Miceuz/linear-led-dimmer/doc/pics/DSC01135.JPG

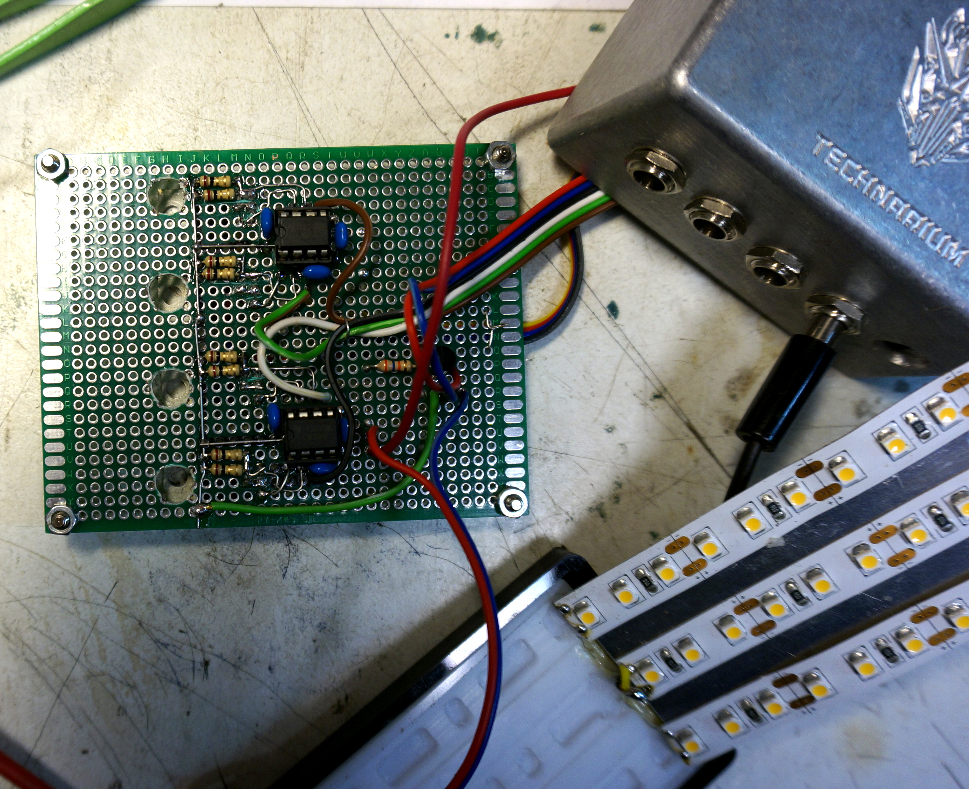
doc/pics/DSC01135.JPG
