Miceuz/linear-led-dimmer/doc/pics/DSC01143.JPG

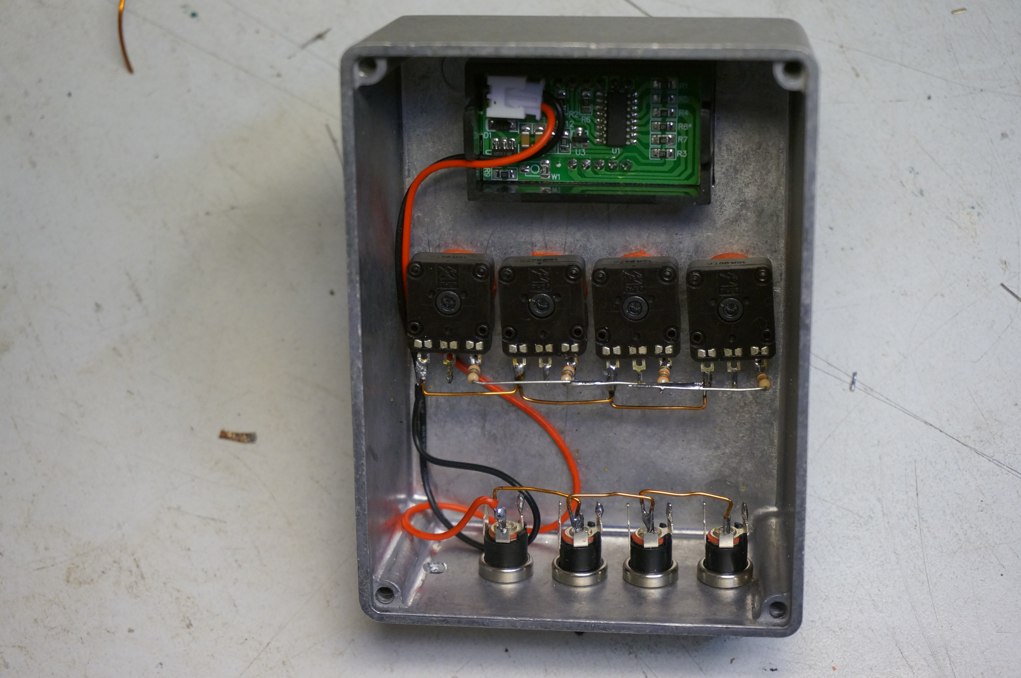
doc/pics/DSC01143.JPG
