Miceuz/linear-led-dimmer/doc/pics/DSC01162.JPG

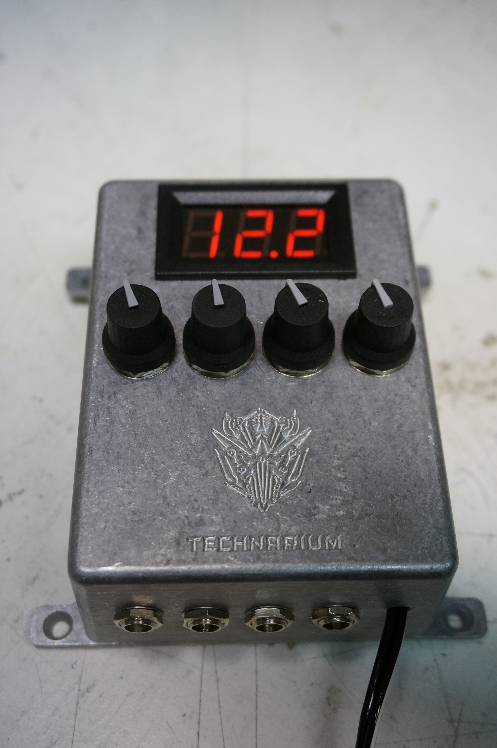
doc/pics/DSC01162.JPG
