Miceuz/linear-led-dimmer/linear-dimmer-back.png

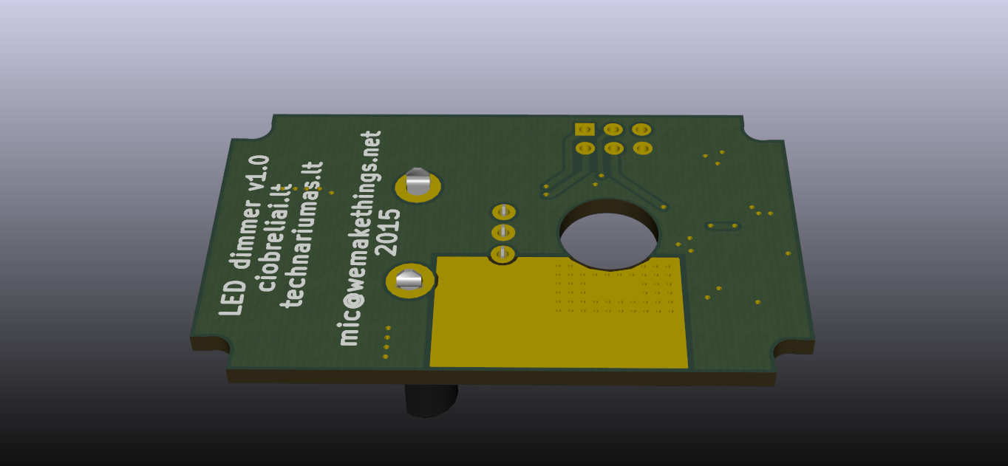
linear-dimmer-back.png
