Miceuz/linear-led-dimmer/linear-dimmer-v2.0-long-edge-conn-back.png

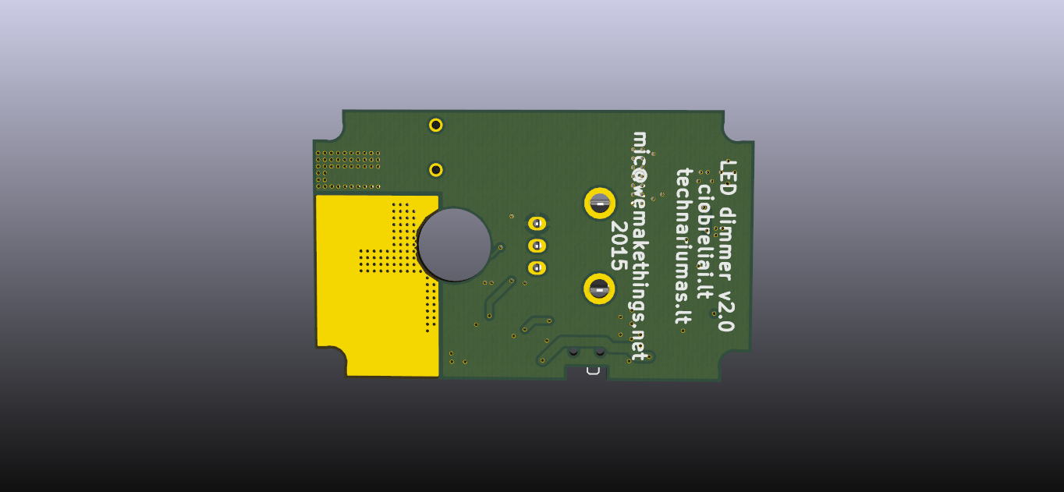
linear-dimmer-v2.0-long-edge-conn-back.png
