Miceuz/linear-led-dimmer/linear-dimmer-v2.0-ortho.png

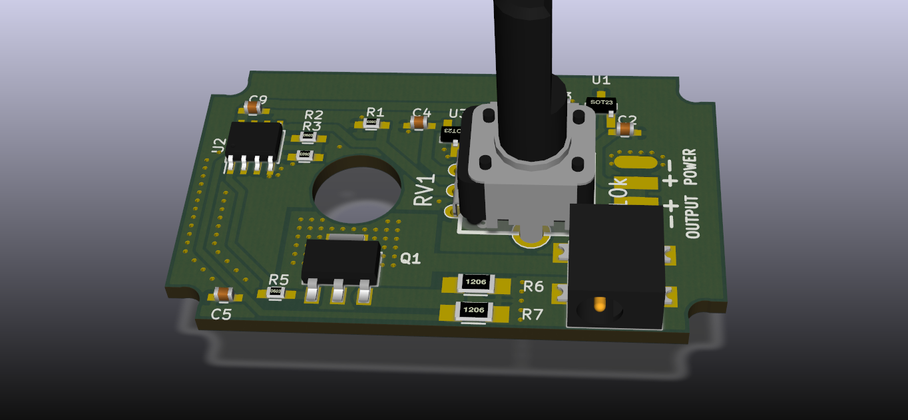
linear-dimmer-v2.0-ortho.png
