Miceuz/linear-led-dimmer/linear-dimmer-v2.0-side.png

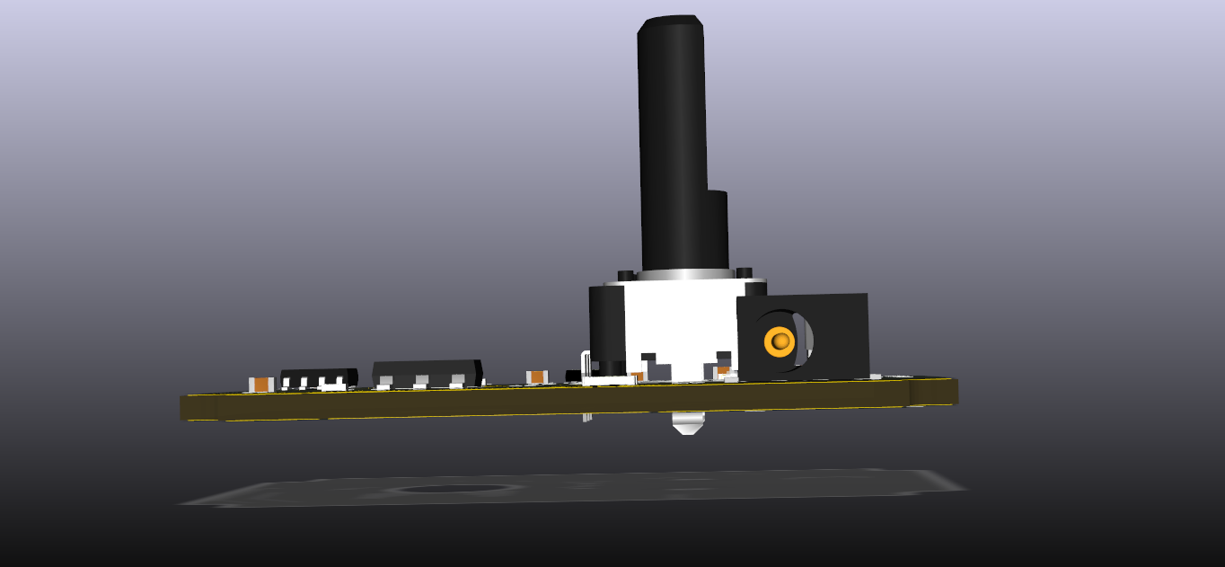
linear-dimmer-v2.0-side.png
