Miceuz/linear-led-dimmer/pannel/pannel replace.png

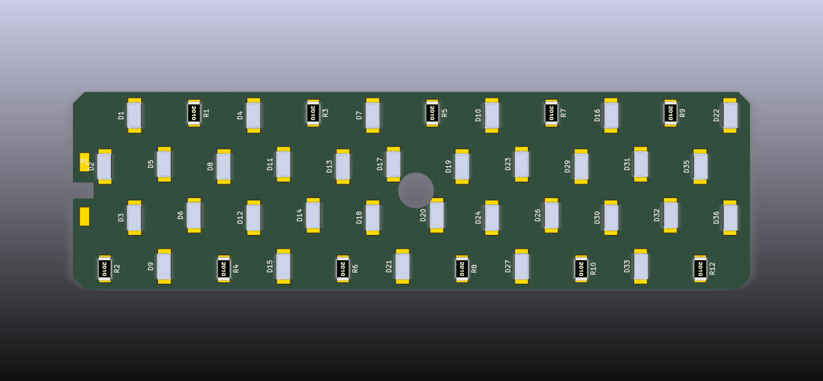
pannel/pannel replace.png
