Miceuz/linear-led-dimmer/pannel/pannel.png

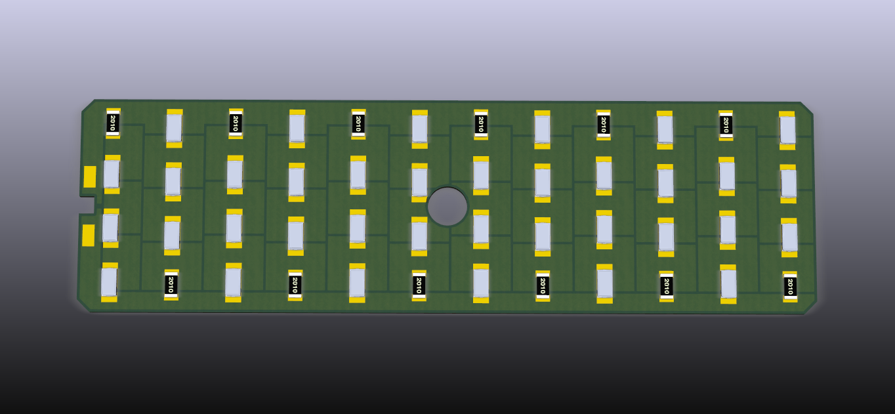
pannel/pannel.png
