Miceuz/linear-led-dimmer/doc/dezute korpusas.pdf

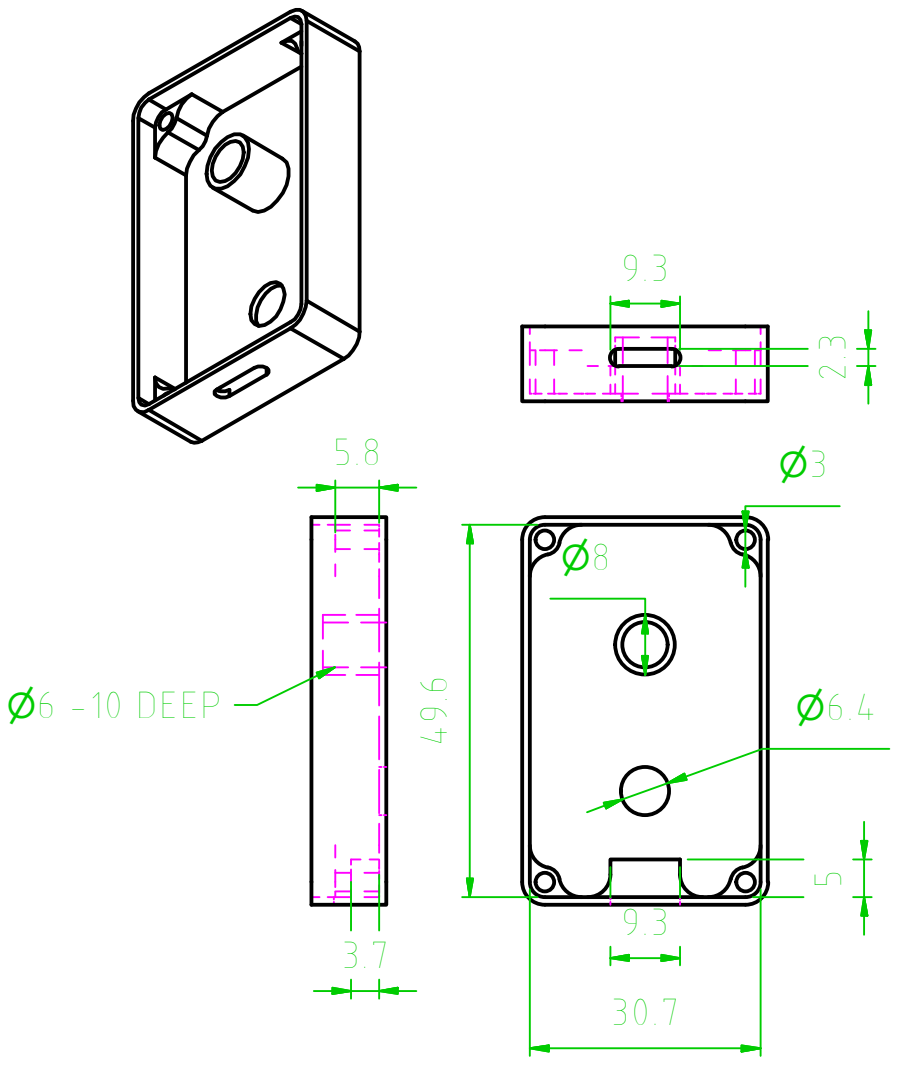
[picture p32: page 1]
P6 -10 DEEP
