Miceuz/linear-led-dimmer/pannel/doc/156x50x10 V7 alu pcb V1-1.pdf

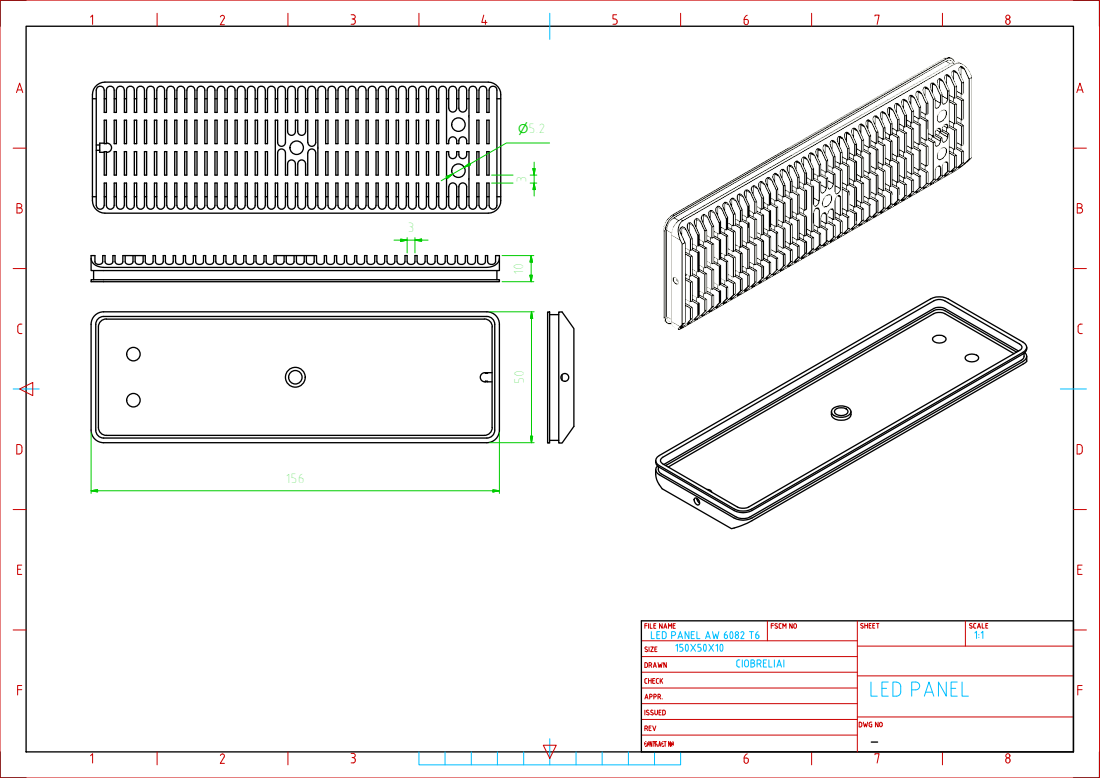
[picture p33: page 1]
