Miceuz/linear-led-dimmer/color-mixer.asc

R1: res; 10k
R2: res; 10k
R3: res; 10k
U1: UniversalOpamp2
V1: voltage; -1
V2: voltage; PULSE(0 1 0 1 1 0 0 1)
V3: voltage; 12
V4: voltage; 2
Named nets: 0, out
.tran 2
