Miceuz/linear-led-dimmer/nonlinear_pot.asc

R1: res; 0
R2: res; R=10k*(1-V(pot_pos))
R3: res; R=10k*V(pot_pos)
R4: res; 2k
R5: res; 36k
R6: res; 10k
V1: voltage; 1.2V
V2: voltage; 1
Named nets: 0, wiper, pot_pos, out
.dc V2 0.01 0.99 0.001
