Miceuz/linear-led-dimmer/Draft2.asc

C1: cap; 10µ
C2: cap; 220µ
D1: LED; LXHL-BW02
D2: schottky; 1N5819
L1: ind; 820µH
M1: nmos; 2N7002
Q1: pnp; 2SAR512P
R1: res; 0.5
R2: res; 1k
U1: LT1721
V1: voltage; 16V
V2: voltage; 0.01
V3: voltage; 5V
Named nets: 0
.tran 0 420e-6 42e-6
